olkal/CG_scale/STL print files/CG_scale_rear_support.stl

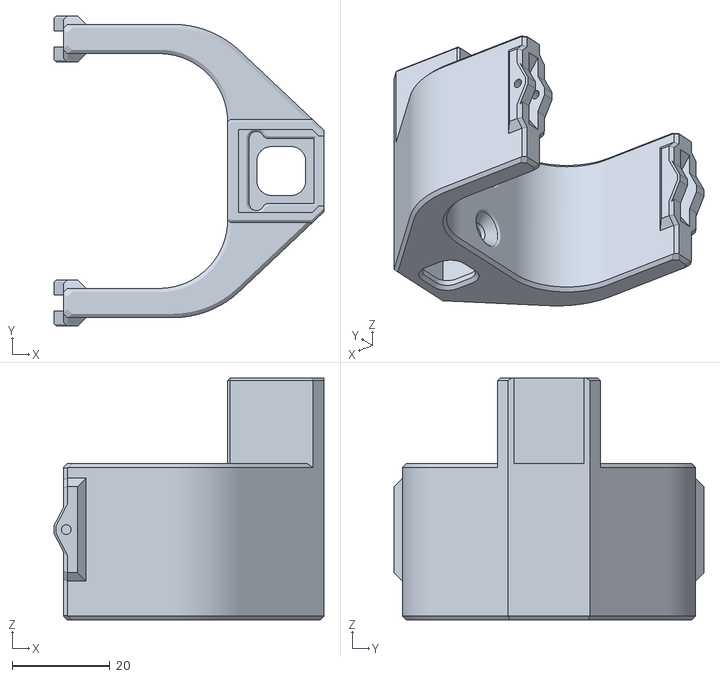
[picture p21: CAD file, 2017-04-18]
STL print files/CG_scale_rear_support.stl
55.2 x 63.4 x 49.5
