olkal/CG_scale/STL print files/CG_scale_framecover_f3f.stl

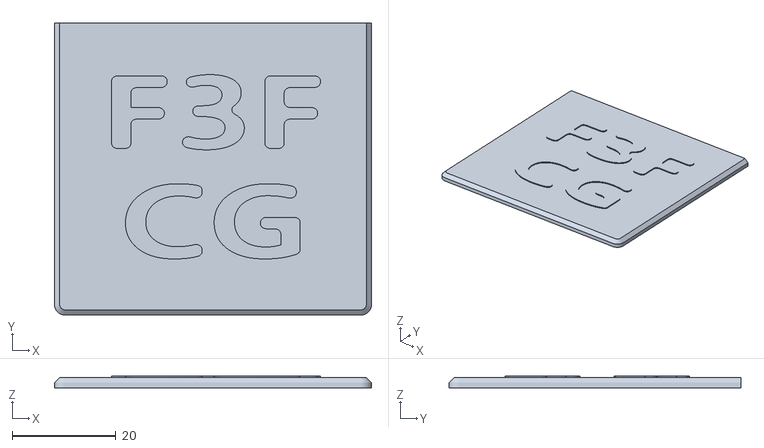
[picture p22: CAD file, 2017-04-18]
STL print files/CG_scale_framecover_f3f.stl
61.0 x 56.2 x 2.25
