olkal/CG_scale/STL print files/CG_scale_frame.stl

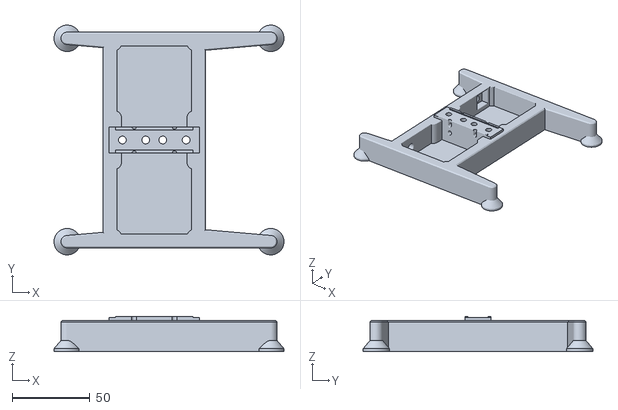
[picture p23: CAD file, 2017-04-18]
STL print files/CG_scale_frame.stl
148.0 x 147.9 x 22.8
